palette-system/az-esportho/images/DSC_1568.jpg

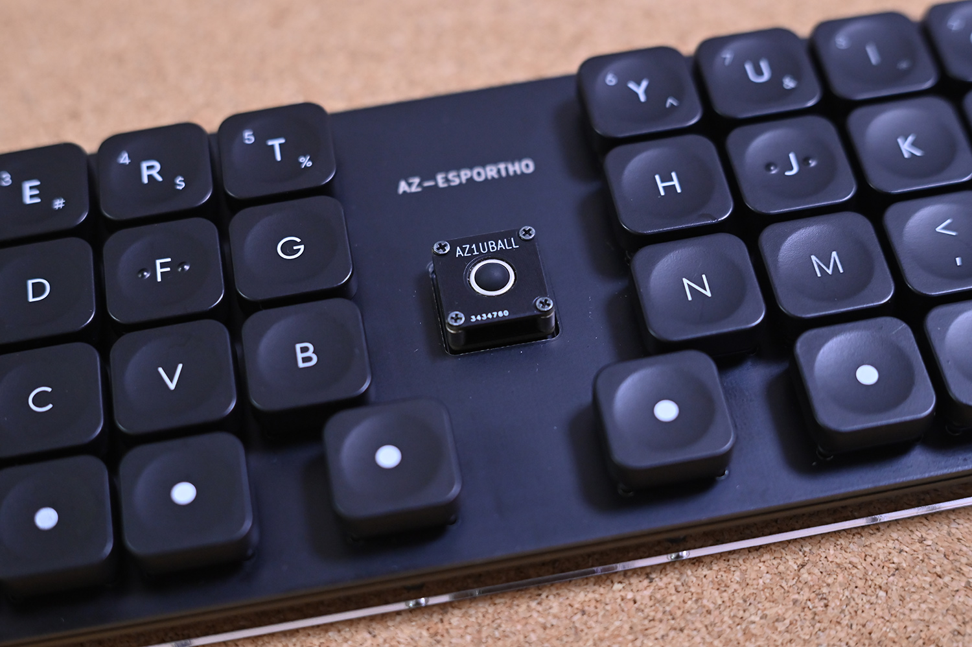
images/DSC_1568.jpg
